ZGQ-inc/3.98-epd/src/display/crc.rs

// src/display/crc.rs — Framebuffer CRC32 Checksum for Persistent State Verification

use crate::display::framebuffer::Framebuffer;

/// Computes standard IEEE 802.3 CRC32 of the 105,984-byte framebuffer.
/// Takes ~1ms on ESP32-C3 at 160MHz.
pub fn compute_fb_crc(fb: &Framebuffer) -> u32 {
    let mut crc: u32 = 0xFFFFFFFF;
    for &b in fb.as_slice() {
        crc ^= b as u32;
        for _ in 0..8 {
            let mask = if (crc & 1) != 0 { 0xEDB88320 } else { 0 };
            crc = (crc >> 1) ^ mask;
        }
    }
    !crc
}
